selmavangstein/bluetooth-tracking-ultimate/merged_results.csv

timestamp | b1d_x | b2d_x | b3d_x | b4d_x | wearabletimestamp | b1d_y | b2d_y | b3d_y | b4d_y | xa | ya | za | ta | Error1 | Error2 | Error3 | Error4
1900-01-01 22:24:40 | 15.03 | 19.95 | 23.5 | 19.49 | 98627 | 14.598862172089854 |  | 23.412295010193848 | 19.094618552083357 | 9.92 | -0.19 | 4.94 | 14.920123994122838 | -0.43113782791014543 |  | -0.08770498980615216 | -0.3953814479166411
1900-01-01 22:24:44 | 17.41 | 17.41 | 21.38 | 21.38 | 102607 | 15.986226243957148 | 18.29212265228781 | 22.17026062384993 | 20.439728456719727 | 9.45 | 1.09 | 4.7 | 13.684173340030446 | -1.423773756042852 | 0.8821226522878085 | 0.7902606238499317 | -0.9402715432802715
1900-01-01 22:24:52 | 19.95 | 15.03 | 19.49 | 23.5 | 110565 | 18.737883743513002 | 15.740732248403761 | 20.145148215293144 | 22.629080097651535 | 9.64 | -1.33 | 5.09 | 15.579300369400418 | -1.212116256486997 | 0.7107322484037617 | 0.6551482152931456 | -0.8709199023484651
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
