selmavangstein/bluetooth-tracking-ultimate/oldstuff/distance-testing/data/oct14fmt.csv

timestamp | distance | interval
10:47:15.391 | 2.1 | 14
10:47:15.391 | 2.4 | 16
10:47:15.391 | 2.4 | 16
10:47:15.391 | 2.55 | 17
10:47:15.391 | 2.1 | 14
10:47:15.391 | 1.95 | 13
10:47:15.391 | 1.95 | 13
10:47:15.391 | 2.1 | 14
10:47:15.391 | 1.95 | 13
10:47:15.508 | 1.95 | 13
10:47:15.816 | 2.25 | 15
10:47:16.123 | 1.2 | 8
10:47:16.429 | 2.1 | 14
10:47:16.724 | 1.95 | 13
10:47:17.032 | 1.65 | 11
10:47:17.351 | 1.95 | 13
10:47:17.659 | 3.6 | 24
10:47:17.951 | 3.15 | 21
10:47:18.273 | 3.0 | 20
10:47:18.566 | 2.7 | 18
10:47:18.880 | 4.35 | 29
10:47:19.180 | 5.25 | 35
10:47:19.502 | 5.7 | 38
10:47:19.781 | 3.75 | 25
10:47:20.391 | 3.75 | 25
10:47:20.391 | 4.5 | 30
10:47:20.697 | 3.75 | 25
10:47:21.007 | 4.05 | 27
10:47:21.312 | 3.75 | 25
10:47:21.605 | 4.5 | 30
10:47:21.913 | 4.2 | 28
10:47:22.528 | 6.15 | 41
10:47:22.528 | 4.35 | 29
10:47:22.848 | 4.35 | 29
10:47:23.155 | 4.95 | 33
10:47:23.462 | 6.15 | 41
10:47:23.758 | 8.25 | 55
10:47:24.069 | 9.0 | 60
10:47:24.384 | 7.05 | 47
10:47:24.693 | 6.75 | 45
10:47:24.999 | 6.75 | 45
10:47:25.613 | 8.1 | 54
10:47:25.613 | 7.05 | 47
10:47:25.919 | 7.35 | 49
10:47:26.215 | 7.95 | 53
10:47:26.535 | 6.6 | 44
10:47:26.843 | 6.6 | 44
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
