selmavangstein/bluetooth-tracking-ultimate/oldstuff/distance-testing/data/oct14realdistance.csv

distance | time
5 | 10:47:31
5 | 10:47:41
10 | 10:47:54
10 | 10:47:54
10 | 10:48:04
15 | 10:48:28
15 | 10:48:28
15 | 10:48:38
20 | 10:48:42
20 | 10:48:42
20 | 10:48:52
25 | 10:49:05
25 | 10:49:05
25 | 10:49:15
30 | 10:49:26
30 | 10:49:26
30 | 10:49:36
